toddzebert/SAOut-Of-This-World/firmware/include/effects.h

#ifndef EFFECTS_H_
#define EFFECTS_H_

// This file just to collect all the effects as a convenience.

#include "effects/ws_blink.h"
#include "effects/raw.h"
#include "effects/twinkle.h"
#include "effects/ws_comet.h"
#include "effects/ws_rotate.h"

#endif /* EFFECTS_H_ */
