toddzebert/SAOut-Of-This-World/firmware/include/things.h

#ifndef THINGS_H_
#define THINGS_H_

// This file just to collect all the things as a convenience.

#include "things/eyes.h"
#include "things/stars.h"
#include "things/upper_trim.h"
#include "things/lower_trim.h"

#endif /* THINGS_H_ */
